LucaSpataru/TSC_project/Images/Alignment_1.png

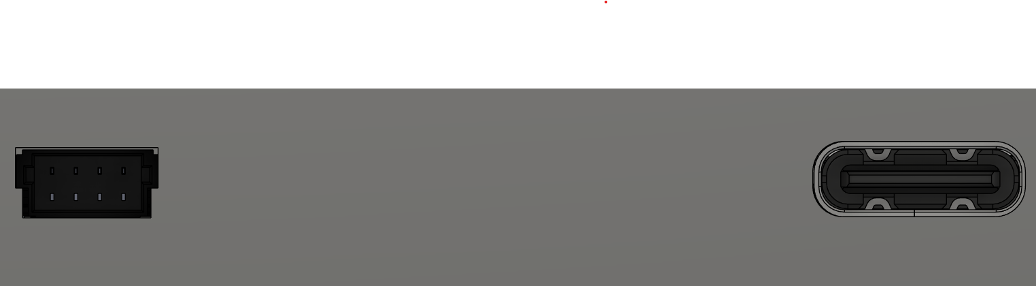
Images/Alignment_1.png
