LucaSpataru/TSC_project/Images/buttons_mod.png

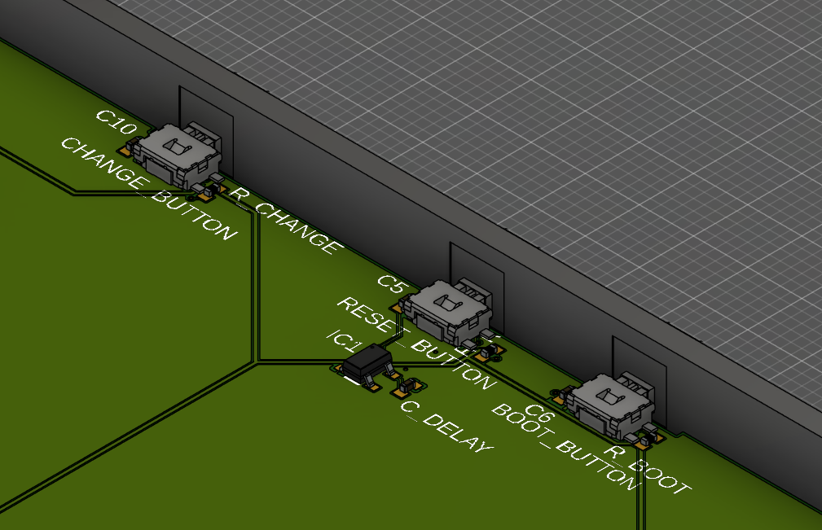
Images/buttons_mod.png
