LucaSpataru/TSC_project/Images/Display.png

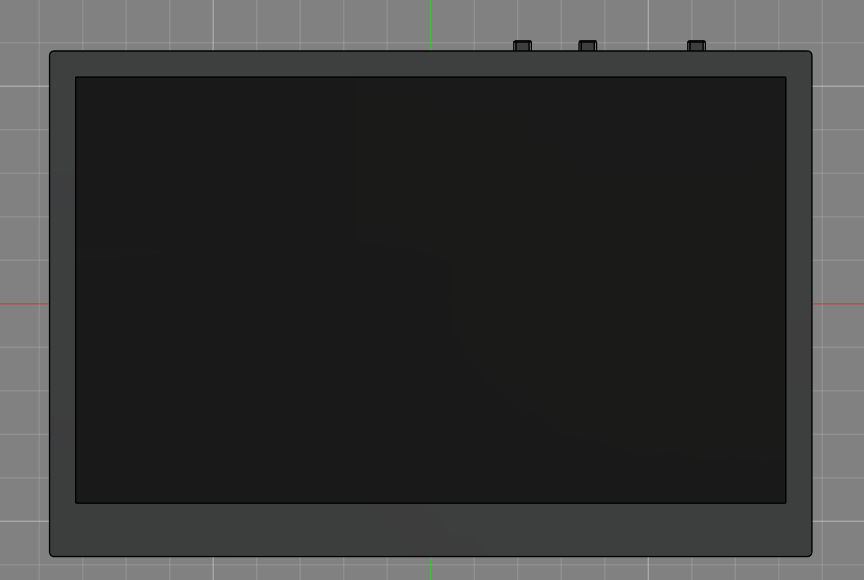
Images/Display.png
