LucaSpataru/TSC_project/Images/NoDisplay.png

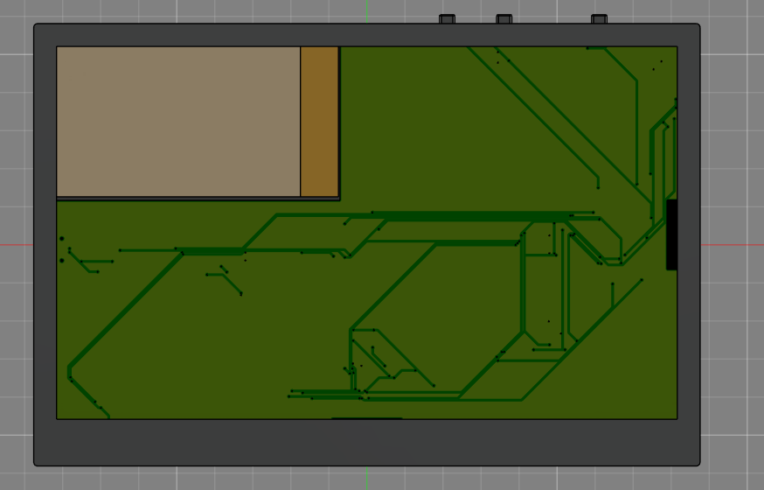
Images/NoDisplay.png
