LucaSpataru/TSC_project/Images/OpenBookDiagram.PNG

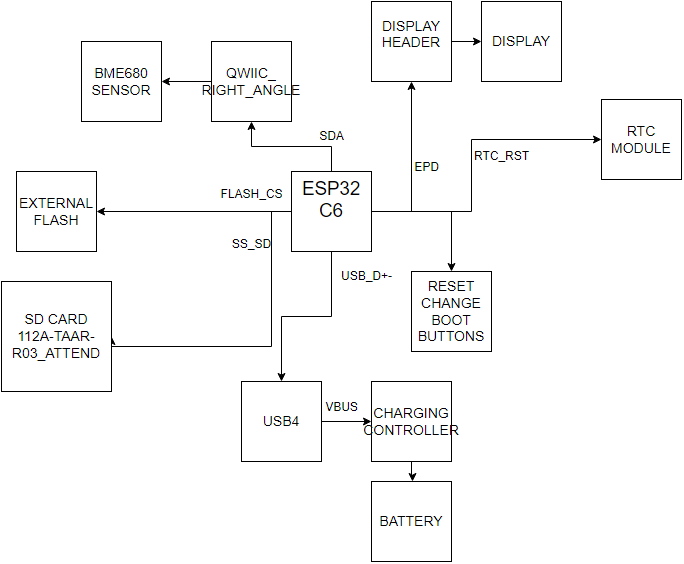
Images/OpenBookDiagram.PNG
