LucaSpataru/TSC_project/Images/PCB_n_battery.png

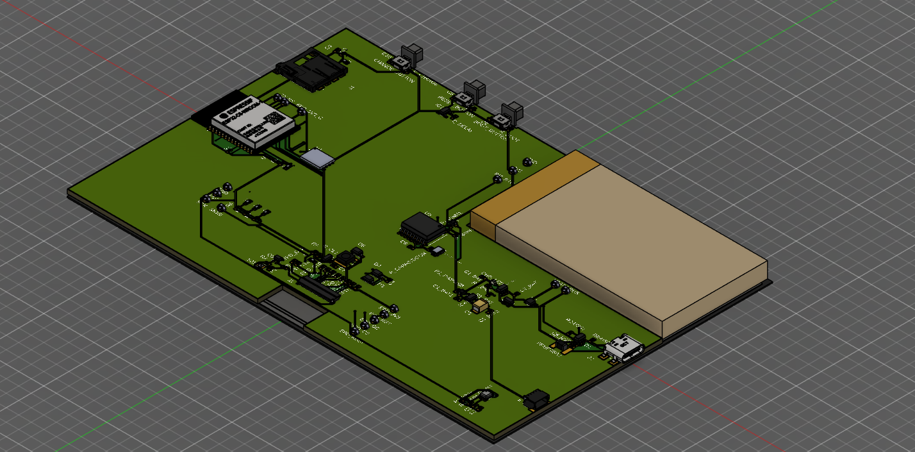
Images/PCB_n_battery.png
